NTNU-TDT4295/BRICOLEUR/accelerators/src/test/scala/helpers/Downscale/gray.png

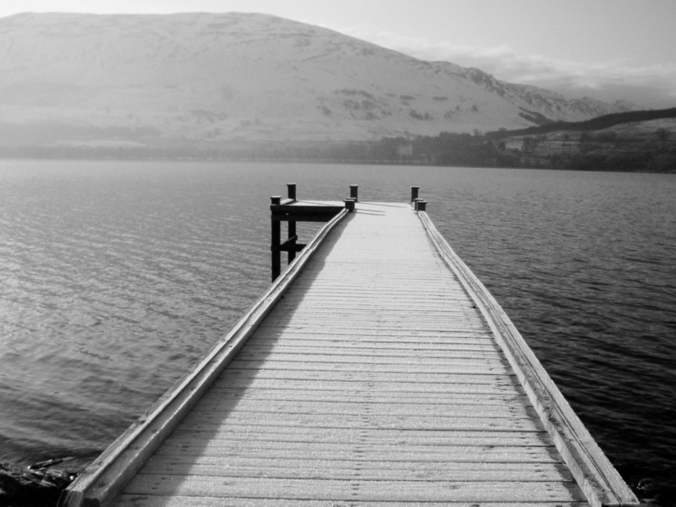
accelerators/src/test/scala/helpers/Downscale/gray.png
