NTNU-TDT4295/BRICOLEUR/DetectionAlgorithm/TestData/im0001.png

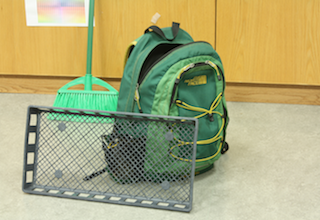
DetectionAlgorithm/TestData/im0001.png
