NTNU-TDT4295/BRICOLEUR/DetectionAlgorithm/TestData/im0002.png

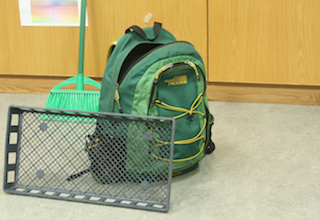
DetectionAlgorithm/TestData/im0002.png
