NTNU-TDT4295/BRICOLEUR/DetectionAlgorithm/TestData/img1.png

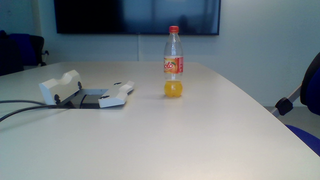
DetectionAlgorithm/TestData/img1.png
