NTNU-TDT4295/BRICOLEUR/DetectionAlgorithm/TestData/img4.png

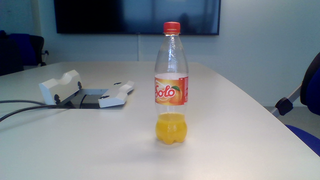
DetectionAlgorithm/TestData/img4.png
