NTNU-TDT4295/BRICOLEUR/DetectionAlgorithm/TestData/img5.png

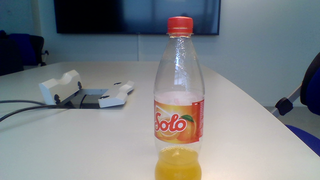
DetectionAlgorithm/TestData/img5.png
