NTNU-TDT4295/BRICOLEUR/DetectionAlgorithm/TestData/img6.png

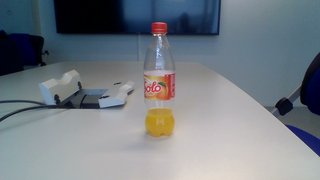
DetectionAlgorithm/TestData/img6.png
