NTNU-TDT4295/BRICOLEUR/DetectionAlgorithm/TestData/IMG_0001.jpg

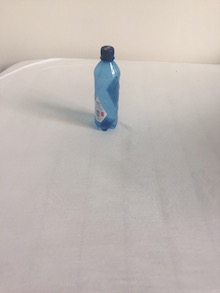
DetectionAlgorithm/TestData/IMG_0001.jpg
