NTNU-TDT4295/BRICOLEUR/DetectionAlgorithm/TestData/IMG_0002.jpg

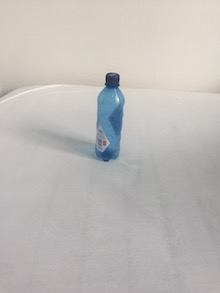
DetectionAlgorithm/TestData/IMG_0002.jpg
