NTNU-TDT4295/BRICOLEUR/DetectionAlgorithm/TestData/IMG_0003.jpg

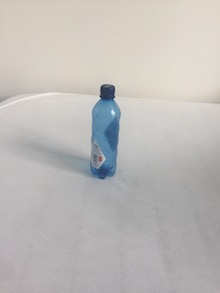
DetectionAlgorithm/TestData/IMG_0003.jpg
