NTNU-TDT4295/BRICOLEUR/DetectionAlgorithm/TestData/IMG_0004.jpg

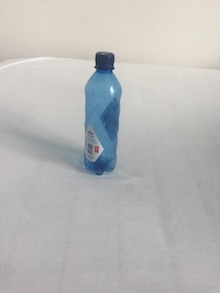
DetectionAlgorithm/TestData/IMG_0004.jpg
