NTNU-TDT4295/BRICOLEUR/DetectionAlgorithm/TestData/IMG_0005.jpg

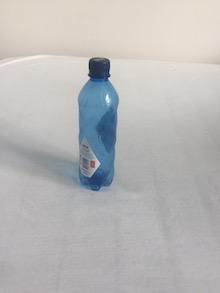
DetectionAlgorithm/TestData/IMG_0005.jpg
