NTNU-TDT4295/BRICOLEUR/DetectionAlgorithm/TestData/IMG_0006.jpg

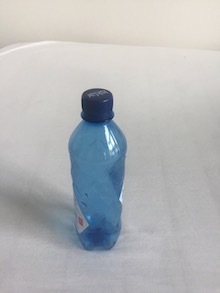
DetectionAlgorithm/TestData/IMG_0006.jpg
